snech99/Cube_Solver_Robot/3D_Model/Halter Magnete v10.step

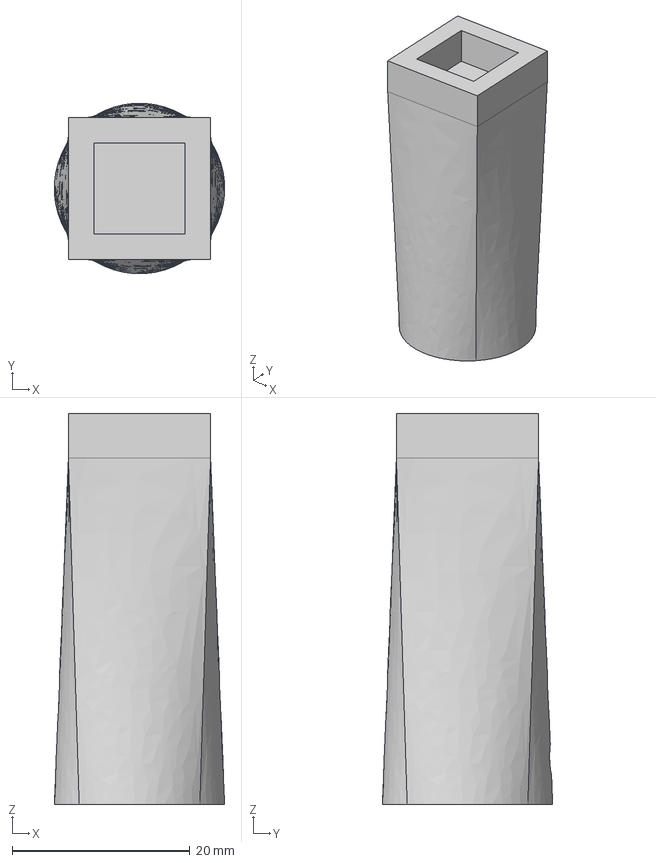
[picture p17: CAD file, 2025-02-12]
3D_Model/Halter Magnete v10.step
19.2 x 19.2 x 44.0 mm
