snech99/Cube_Solver_Robot/3D_Model/Schild v3.step

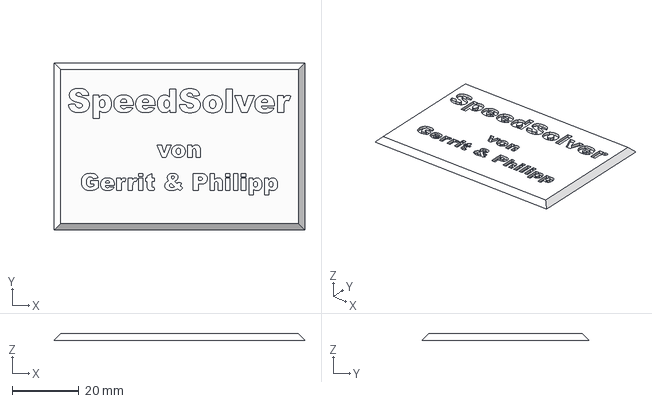
[picture p18: CAD file, 2025-02-12]
3D_Model/Schild v3.step
75.0 x 50.0 x 2.00 mm
