snech99/Cube_Solver_Robot/3D_Model/Halter Reset v4.step

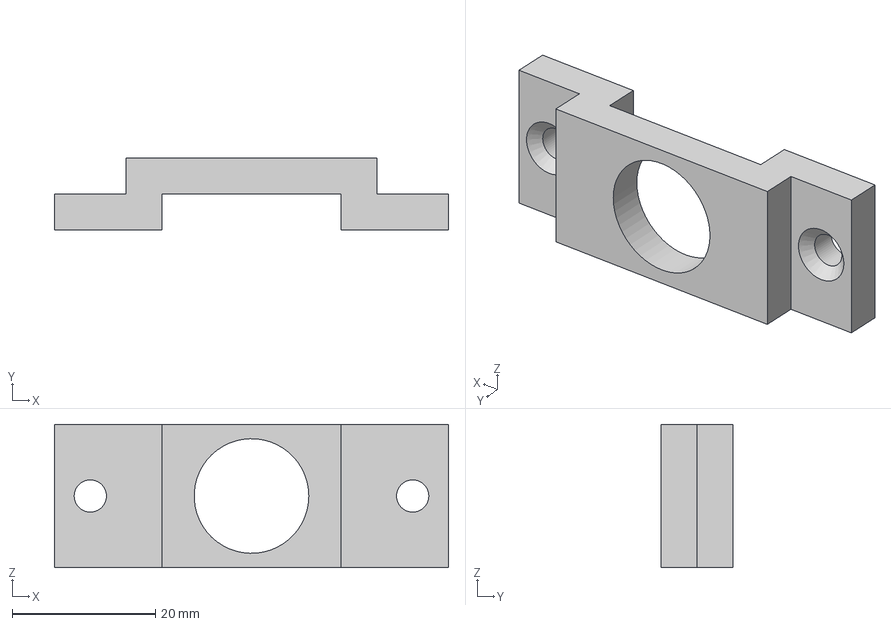
[picture p19: CAD file, 2025-02-12]
3D_Model/Halter Reset v4.step
55.0 x 10.0 x 20.0 mm
