snech99/Cube_Solver_Robot/3D_Model/Abdeckung Netzteil v5.step

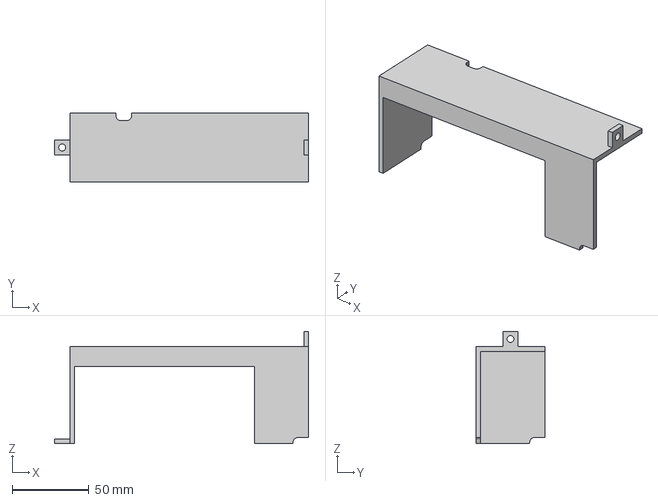
[picture p20: CAD file, 2025-02-12]
3D_Model/Abdeckung Netzteil v5.step
165.0 x 45.0 x 73.0 mm
