snech99/Cube_Solver_Robot/3D_Model/Ecke Aluprofil v8.step

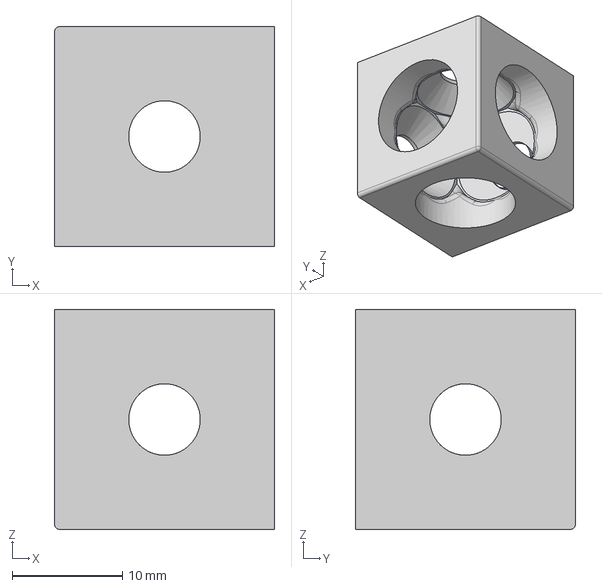
[picture p21: CAD file, 2025-02-12]
3D_Model/Ecke Aluprofil v8.step
20.0 x 20.0 x 20.0 mm
