snech99/Cube_Solver_Robot/3D_Model/Abstandshalter Display v2.step

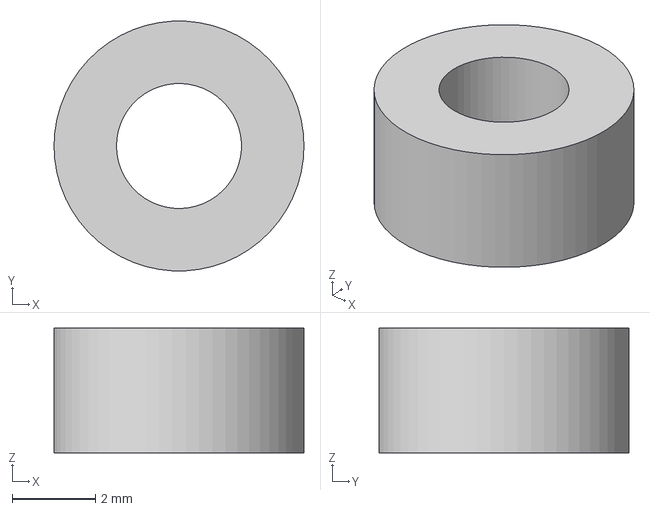
[picture p22: CAD file, 2025-02-12]
3D_Model/Abstandshalter Display v2.step
6.00 x 5.99 x 3.00 mm
