snech99/Cube_Solver_Robot/3D_Model/Wand links_rechts v6.step

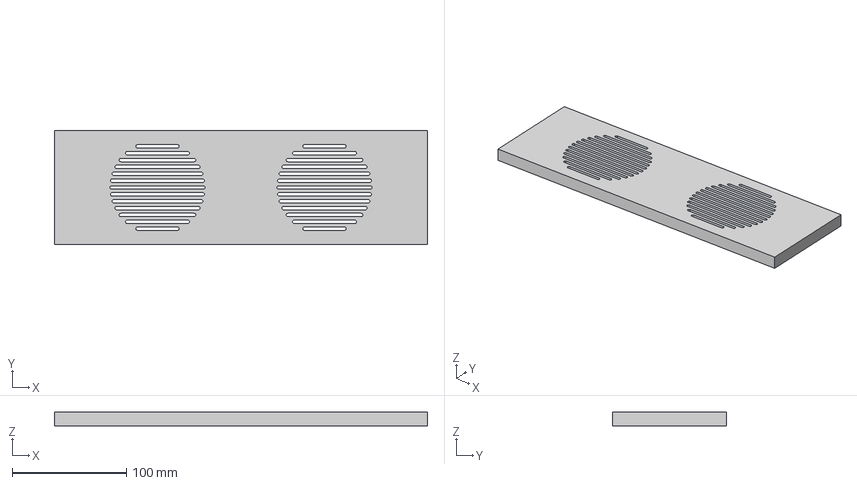
[picture p23: CAD file, 2025-02-12]
3D_Model/Wand links_rechts v6.step
326.0 x 100.0 x 12.0 mm
