snech99/Cube_Solver_Robot/3D_Model/Reset Griff v1.step

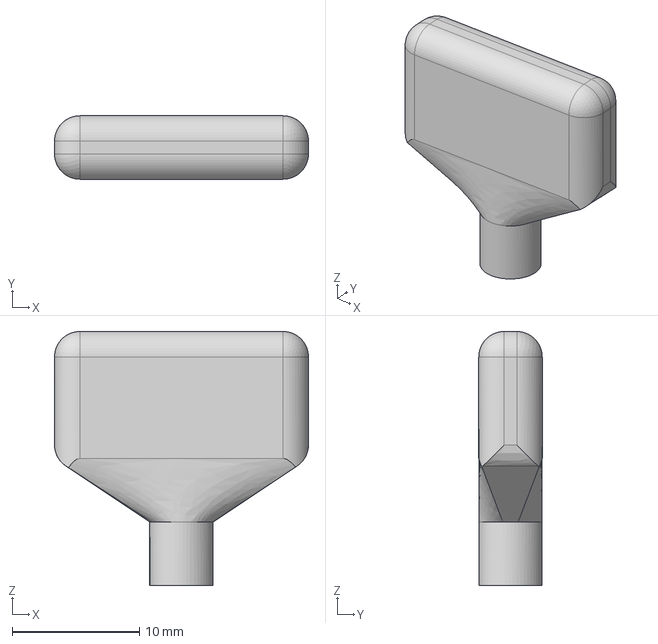
[picture p24: CAD file, 2025-02-12]
3D_Model/Reset Griff v1.step
20.0 x 5.00 x 20.0 mm
