snech99/Cube_Solver_Robot/3D_Model/Versteifung v2.step

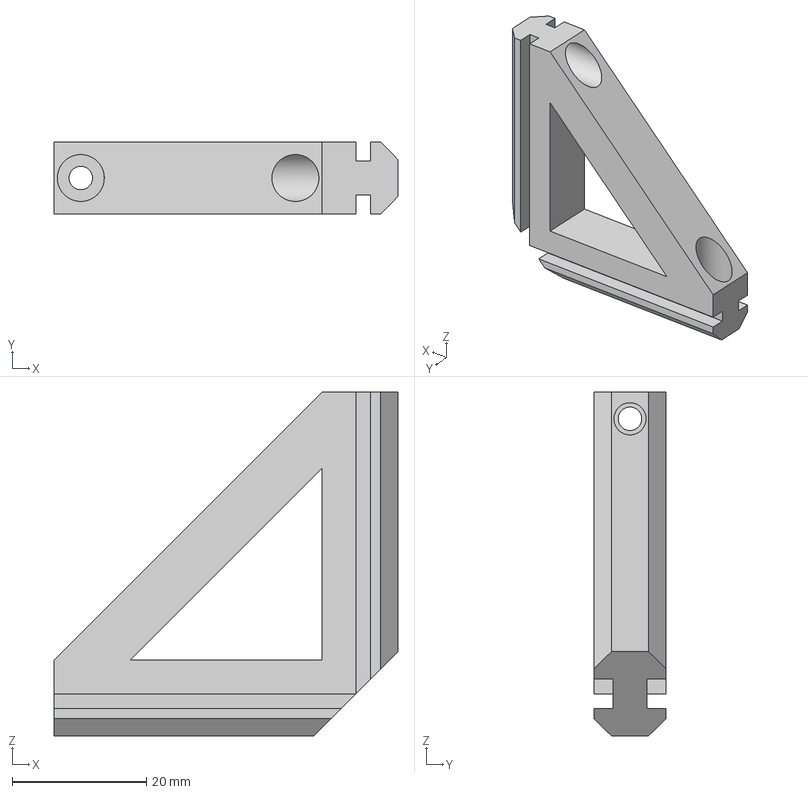
[picture p25: CAD file, 2025-02-12]
3D_Model/Versteifung v2.step
51.3 x 10.8 x 51.3 mm
