snech99/Cube_Solver_Robot/3D_Model/Abdeckung Sensor v7.step

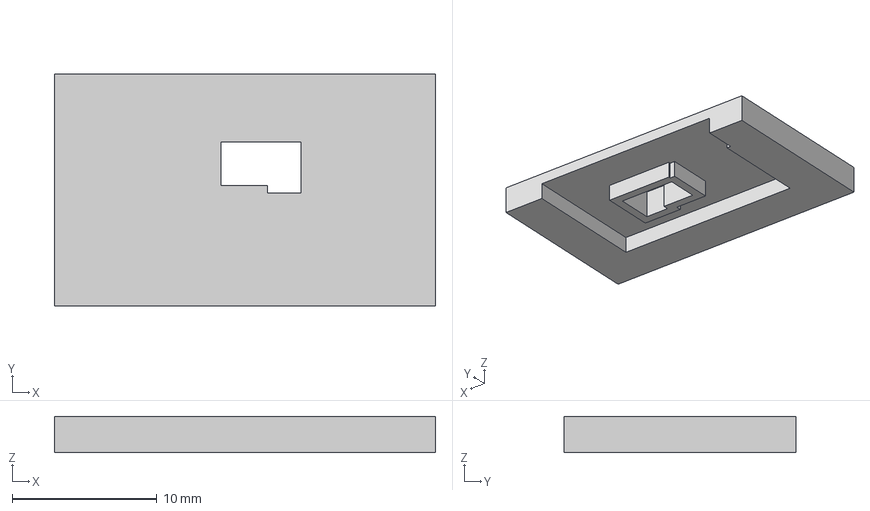
[picture p26: CAD file, 2025-02-12]
3D_Model/Abdeckung Sensor v7.step
26.3 x 16.0 x 2.50 mm
