snech99/Cube_Solver_Robot/3D_Model/Sensorarm v34.step

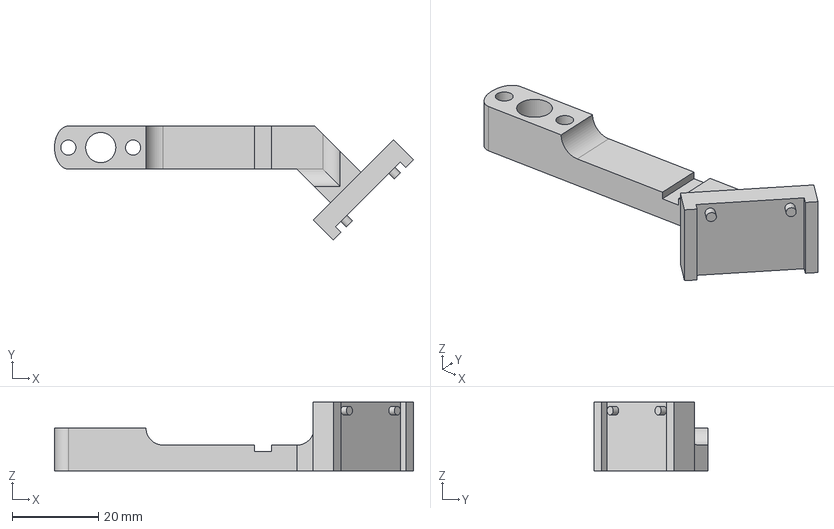
[picture p27: CAD file, 2025-02-12]
3D_Model/Sensorarm v34.step
83.3 x 26.4 x 16.0 mm
