snech99/Cube_Solver_Robot/src/Mikrocontroller/Cube_Project/source/state_machine.h

/*
*   Gerrit Hinrichs 01.2025
*   github.com/snech99
*
*   Cube_Solver_Robot
*   Header State-Machine
*/
#ifndef STATE_MACHINE_H_
#define STATE_MACHINE_H_

typedef enum
{
	config,
	idle_auto,
	random_auto,
	read_color_auto,
	solve_auto,
	change_cube,
	fast,
	slow,
	idle_man,
}State_t;

typedef enum
{
	Taster_T_L,
	Taster_T_R,
	Taster_B_L,
	Taster_B_R,
	msg_random,
	msg_read_color,
	msg_send_cube,
	msg_solve,
	msg_change,
	default_event,
}Event_t;

typedef struct {
    State_t current_state;
    Event_t event;
    State_t next_state;
    void (*action)(void);
} State_Transition;

void auto_to_random_Handler(void);
void auto_to_read_color_Handler(void);
void auto_to_solve_Handler(void);
void auto_to_change_Handler(void);
void solve_to_fast_Handler(void);
void solve_to_slow_Handler(void);
void back_to_auto(void);

void config_to_man_Handler(void);
void man_to_random_Handler(void);
void man_to_read_color_Handler(void);
void man_to_send_cube_Handler(void);
void man_to_solve_Handler(void);
void man_to_change_Handler(void);

void super_machine();

extern Event_t new_event;

#endif
