snech99/Cube_Solver_Robot/src/external_Computer/serial.c

/*
*   Gerrit Hinrichs 01.2025
*   github.com/snech99
*
*   Cube_Solver_Robot
*   file for the USB/UART configuration
*/

#include "serial.h"

int config_serial(int *com)
{
    struct termios tty;

    // Read in existing settings, and handle any error
    if(tcgetattr(*com, &tty) != 0) 
    {
        printf("Error %i from tcgetattr: %s\n", errno, strerror(errno));
        return 1;
    }

    tty.c_cflag &= ~PARENB; // Clear parity bit, disabling parity (most common)
    tty.c_cflag &= ~CSTOPB; // Clear stop field, only one stop bit used in communication (most common)
    tty.c_cflag &= ~CSIZE; // Clear all bits that set the data size
    tty.c_cflag |= CS8; // 8 bits per byte (most common)
    tty.c_cflag &= ~CRTSCTS; // Disable RTS/CTS hardware flow control (most common)
    tty.c_cflag |= CREAD | CLOCAL; // Turn on READ & ignore ctrl lines (CLOCAL = 1)

    tty.c_lflag &= ~ICANON;
    tty.c_lflag &= ~ECHO; // Disable echo
    tty.c_lflag &= ~ECHOE; // Disable erasure
    tty.c_lflag &= ~ECHONL; // Disable new-line echo
    tty.c_lflag &= ~ISIG; // Disable interpretation of INTR, QUIT and SUSP
    tty.c_iflag &= ~(IXON | IXOFF | IXANY); // Turn off s/w flow ctrl
    tty.c_iflag &= ~(IGNBRK|BRKINT|PARMRK|ISTRIP|INLCR|IGNCR|ICRNL); // Disable any special handling of received bytes

    tty.c_oflag &= ~OPOST; // Prevent special interpretation of output bytes (e.g. newline chars)
    tty.c_oflag &= ~ONLCR; // Prevent conversion of newline to carriage return/line feed
    // tty.c_oflag &= ~OXTABS; // Prevent conversion of tabs to spaces (NOT PRESENT ON LINUX)
    // tty.c_oflag &= ~ONOEOT; // Prevent removal of C-d chars (0x004) in output (NOT PRESENT ON LINUX)

    tty.c_cc[VTIME] = 5; // Wait for up to 1s (10 deciseconds), returning as soon as any data is received.
    tty.c_cc[VMIN] = 61; //61

    // Set in/out baud rate to be 115200
    cfsetispeed(&tty, B115200);
    cfsetospeed(&tty, B115200);

    // Save tty settings, also checking for error
    if (tcsetattr(*com, TCSANOW, &tty) != 0) 
    {
        printf("Error %i from tcsetattr: %s\n", errno, strerror(errno));
        return 1;
    }
    return 0;
}
